zjuyzj/OPL2LPT-Replica/images/3.jpg

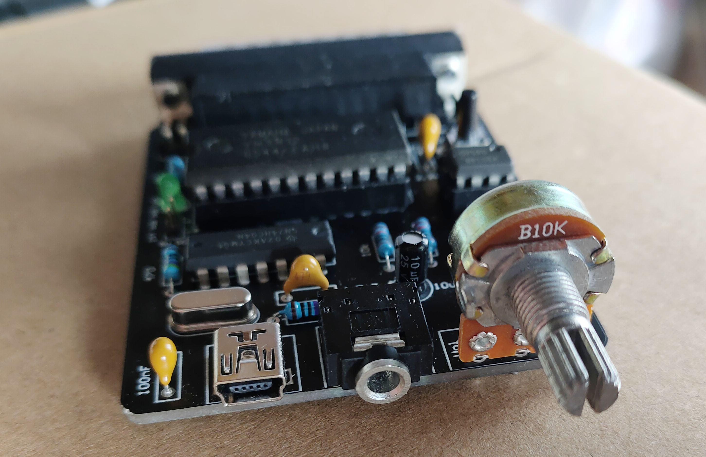
images/3.jpg
