zjuyzj/OPL2LPT-Replica/images/4.jpg

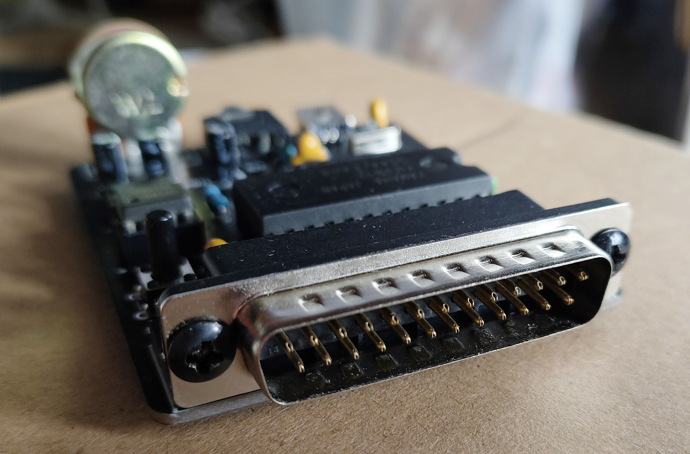
images/4.jpg
